sdfgeoff/LaserRunPistol/Mechanical/CAD/Parts/ElectronicsBay/ElectronicsBayLolin32Lite.stl.FCStd

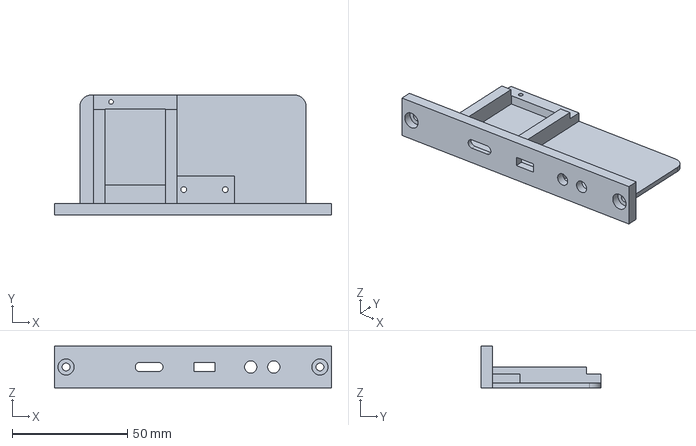
[picture p13: CAD file, 2025-03-06]
Mechanical/CAD/Parts/ElectronicsBay/ElectronicsBayLolin32Lite.stl.FCStd
120.0 x 52.0 x 18.0 mm
