sdfgeoff/LaserRunPistol/Mechanical/CAD/Parts/RearSights/RearSightBase.stl.FCStd

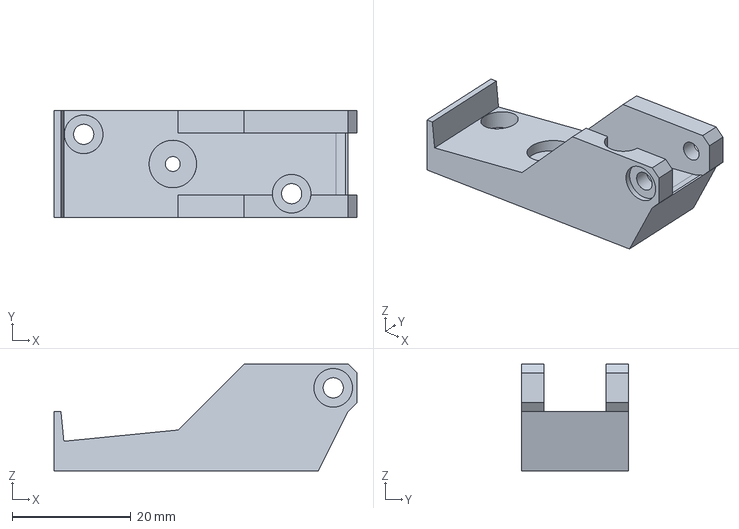
[picture p14: CAD file, 2025-02-21]
Mechanical/CAD/Parts/RearSights/RearSightBase.stl.FCStd
51.0 x 18.0 x 18.0 mm
