sdfgeoff/LaserRunPistol/Mechanical/CAD/Parts/TriggerPlate/TriggerPivotBusing.stl.FCStd

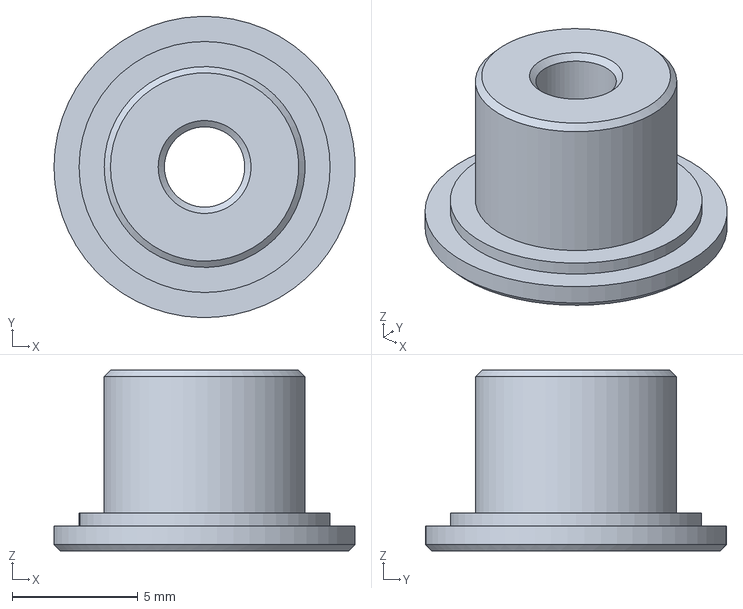
[picture p15: CAD file, 2025-02-22]
Mechanical/CAD/Parts/TriggerPlate/TriggerPivotBusing.stl.FCStd
12.0 x 12.0 x 7.20 mm
