sdfgeoff/LaserRunPistol/Mechanical/CAD/ReferenceParts/LaserModule12mm.FCStd

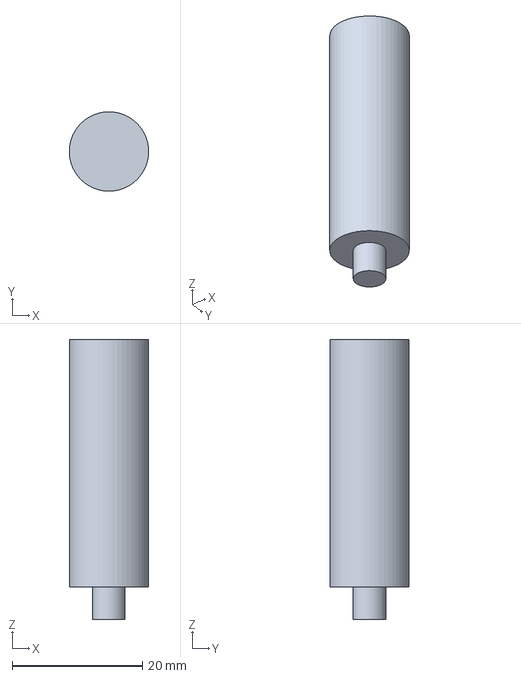
[picture p16: CAD file, 2025-02-22]
Mechanical/CAD/ReferenceParts/LaserModule12mm.FCStd
12.2 x 12.2 x 43.0 mm
