sdfgeoff/LaserRunPistol/Mechanical/CAD/Parts/FrameUpper.stl.FCStd

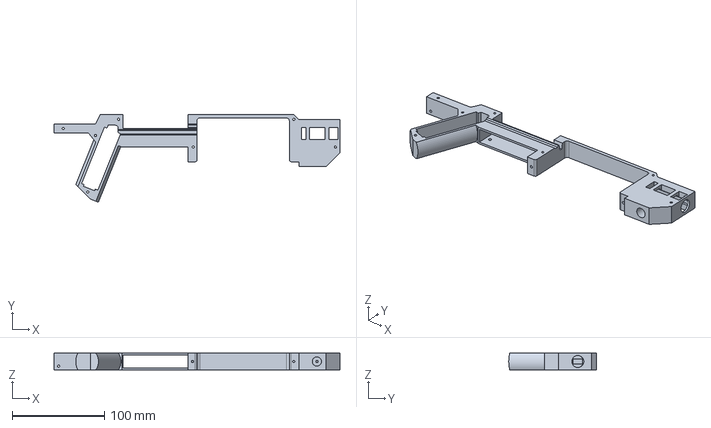
[picture p17: CAD file, 2025-03-06]
Mechanical/CAD/Parts/FrameUpper.stl.FCStd
310.0 x 94.9 x 18.0 mm
