sdfgeoff/LaserRunPistol/Mechanical/CAD/ReferenceParts/M3.FCStd

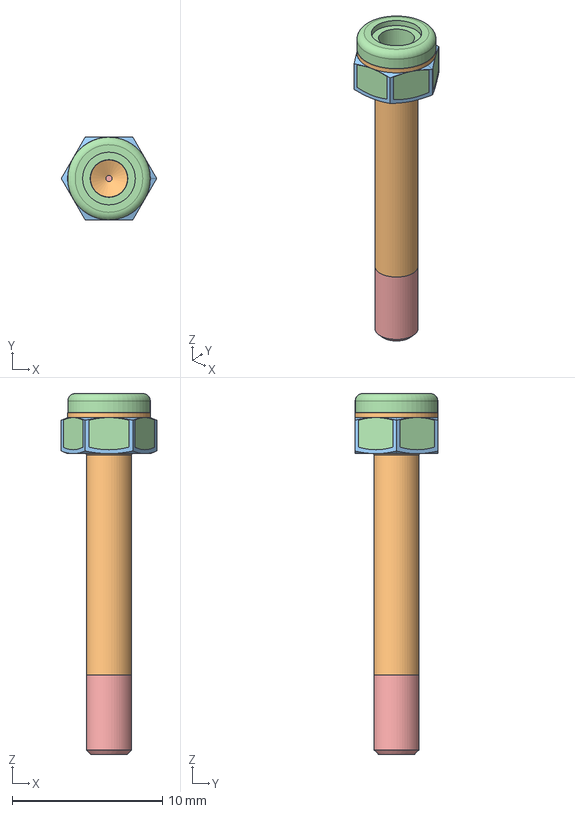
[picture p18: CAD file, 2025-02-22]
Mechanical/CAD/ReferenceParts/M3.FCStd
6.35 x 5.50 x 24.0 mm
M3x10-Screw
M3x15-Screw
M3-Nut
M3-Nut001
M3x20-Screw
