sdfgeoff/LaserRunPistol/Mechanical/CAD/Parts/Handgrip.stl.FCStd

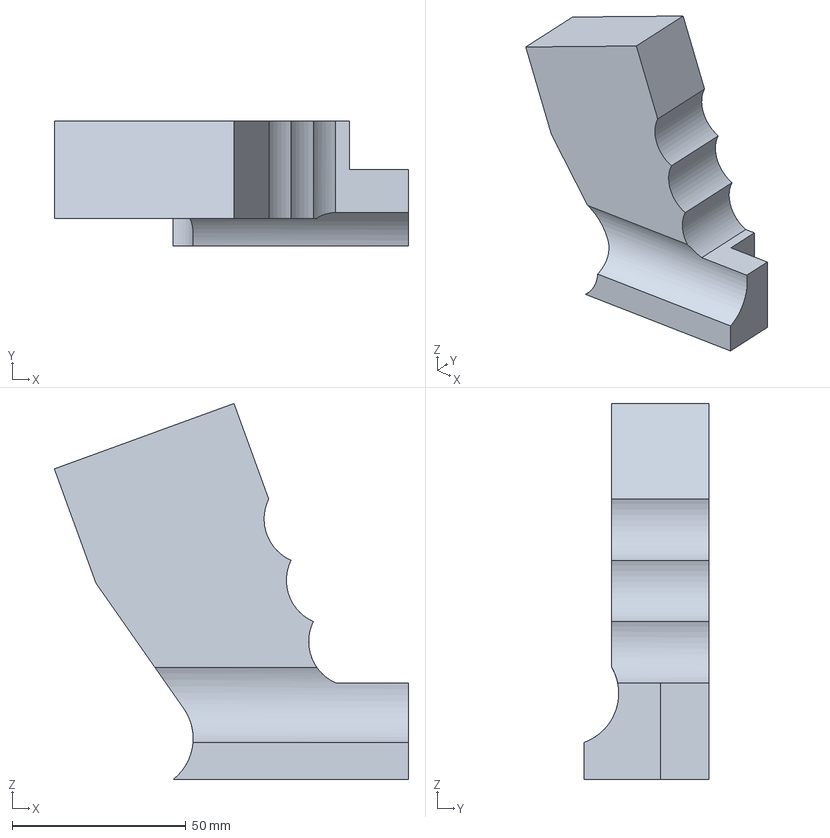
[picture p19: CAD file, 2025-02-27]
Mechanical/CAD/Parts/Handgrip.stl.FCStd
101.9 x 36.0 x 108.2 mm
