sdfgeoff/LaserRunPistol/Mechanical/CAD/Parts/TriggerPlate/Trigger.stl.FCStd

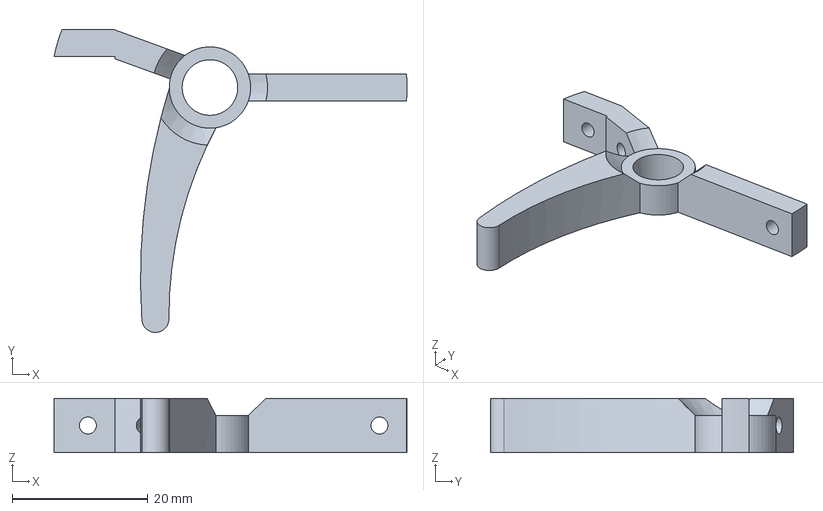
[picture p20: CAD file, 2025-02-22]
Mechanical/CAD/Parts/TriggerPlate/Trigger.stl.FCStd
52.1 x 44.7 x 8.00 mm
