sdfgeoff/LaserRunPistol/Mechanical/CAD/ReferenceParts/M2.FCStd

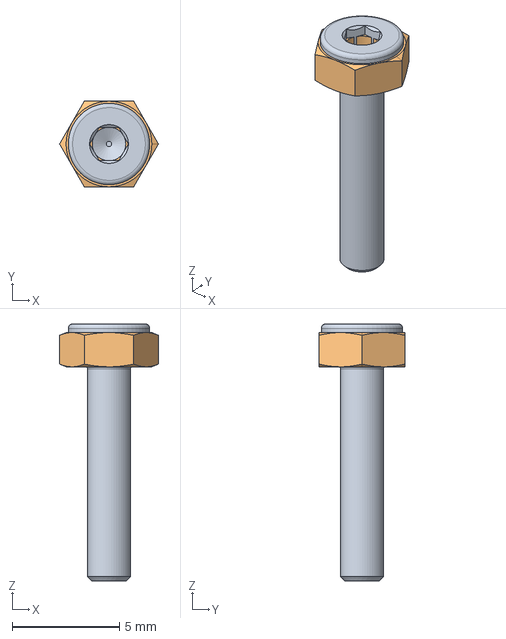
[picture p21: CAD file, 2025-02-22]
Mechanical/CAD/ReferenceParts/M2.FCStd
4.62 x 4.00 x 12.0 mm
M2x10-Screw
M2-Nut
