sdfgeoff/LaserRunPistol/Mechanical/CAD/Parts/TriggerPlate/LoadingLever.stl.FCStd

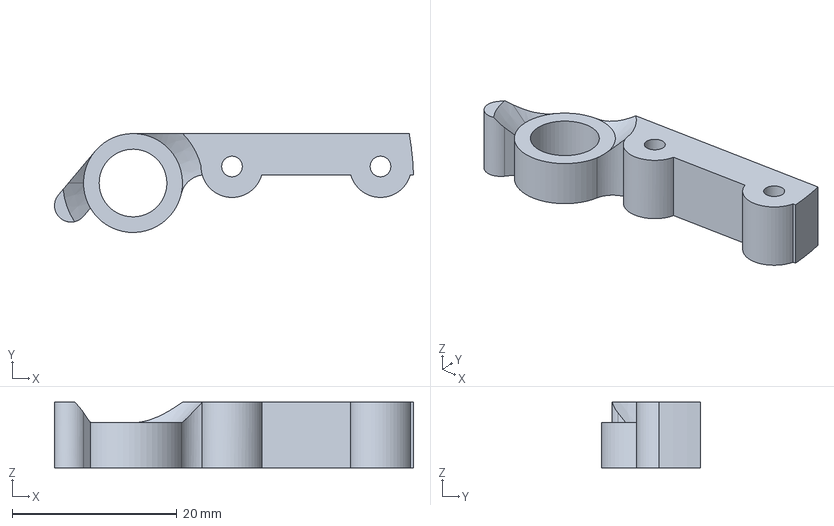
[picture p22: CAD file, 2025-02-22]
Mechanical/CAD/Parts/TriggerPlate/LoadingLever.stl.FCStd
43.5 x 12.0 x 8.00 mm
