sdfgeoff/LaserRunPistol/Mechanical/CAD/Parts/SizeRequirements.FCStd

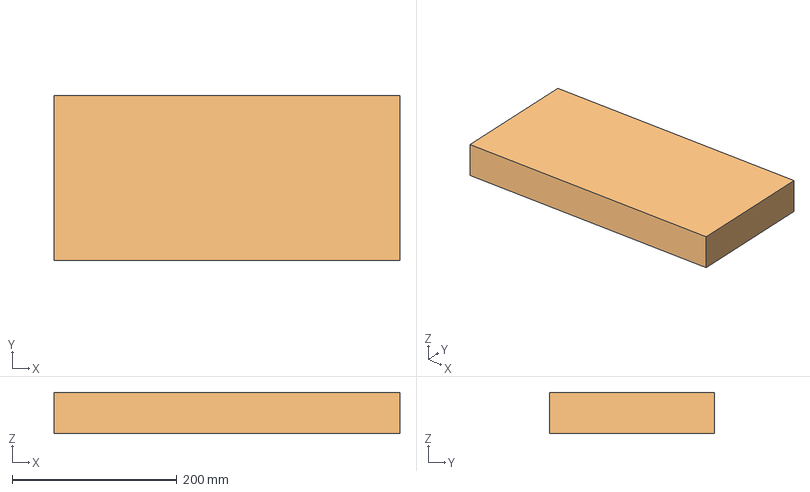
[picture p23: CAD file, 2025-02-22]
Mechanical/CAD/Parts/SizeRequirements.FCStd
420.0 x 200.0 x 50.0 mm
Size Requirement Min
Size Requirement Max
