sdfgeoff/LaserRunPistol/Mechanical/CAD/Parts/FrontSight.stl.FCStd

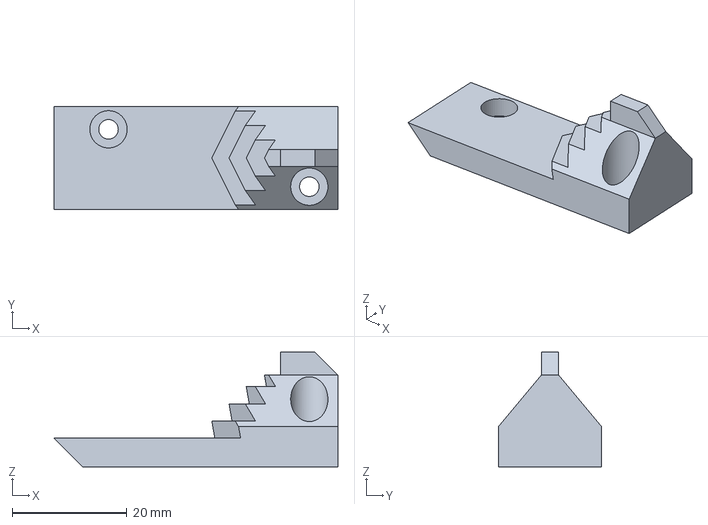
[picture p24: CAD file, 2025-02-21]
Mechanical/CAD/Parts/FrontSight.stl.FCStd
49.5 x 18.0 x 20.0 mm
